fpga-design-contest/ad-refkit/zybo/ROOT_FS/app/motor-test-websocket/src/main.h

/**
 *  motor-test:
 *
 *  Copyright (C) 2020 Yuya Kudo.
 *  Authors:
 *      Yuya Kudo <ri0049ee@ed.ritsumei.ac.jp>
 *
 */

#ifndef MOTOR_TEST_SRC_MAIN_H_
#define MOTOR_TEST_SRC_MAIN_H_

#include <zynqpl.h>

#endif /* MOTOR_TEST_SRC_MAIN_H_ */
